Destination-SPACE/DS-Weather-Station-V4.5/docs/software/demo.rst

.. Copyright 2024 Destination SPACE Inc.
   Licensed under the Apache License, Version 2.0 (the "License");
   you may not use this file except in compliance with the License.
   You may obtain a copy of the License at

      http://www.apache.org/licenses/LICENSE-2.0

   Unless required by applicable law or agreed to in writing, software
   distributed under the License is distributed on an "AS IS" BASIS,
   WITHOUT WARRANTIES OR CONDITIONS OF ANY KIND, either express or implied.
   See the License for the specific language governing permissions and
   limitations under the License.

.. _demo-sketch:

Demo Sketch
===========

The `Demo <https://gitlab.com/Destination-SPACE/ds-weather-station-v4.5/-/blob/main/software/Demo/Demo.ino>`_ sketch is used as an introductory program to most of the features on the weather station. This includes scrollable menus for all sensors.

There is no data recording in this example.

Button Menu
-----------

On the weather station there are 4 buttons, ↑, ↓, ←, →.

The ← and → buttons are used to scroll between the weather menu, air quality menu, and the light menu.
