Destination-SPACE/DS-Weather-Station-V4.5/docs/activities/temperature.rst

.. Copyright 2024 Destination SPACE Inc.
   Licensed under the Apache License, Version 2.0 (the "License");
   you may not use this file except in compliance with the License.
   You may obtain a copy of the License at

      http://www.apache.org/licenses/LICENSE-2.0

   Unless required by applicable law or agreed to in writing, software
   distributed under the License is distributed on an "AS IS" BASIS,
   WITHOUT WARRANTIES OR CONDITIONS OF ANY KIND, either express or implied.
   See the License for the specific language governing permissions and
   limitations under the License.

.. _temperature:

Temperature Activity - Microclimates
====================================

Duration: 15 minutes

Background
----------

Materials
---------

- Destination Weather Station
- Paper
- Pencil

Procedure
---------

1. Make a map of the classroom on a sheet of paper. Make sure to label any windows, doors, air vents, and significant heat sources.
2. Make a prediction for which areas of the classroom you think will be hot or cold.
3. On your map, mark locations in the classroom you want to collect data.
4. Using your weather station, record the average temperature at each location you marked on your map.

Discussion Questions
--------------------

1. Did your predictions match the data you collected? Why might they be different?
2. What do you think caused that part of the classroom to be that temperature?
