Destination-SPACE/DS-Weather-Station-V4.5/docs/sensors/index.rst

.. Copyright 2024 Destination SPACE Inc.
   Licensed under the Apache License, Version 2.0 (the "License");
   you may not use this file except in compliance with the License.
   You may obtain a copy of the License at

      http://www.apache.org/licenses/LICENSE-2.0

   Unless required by applicable law or agreed to in writing, software
   distributed under the License is distributed on an "AS IS" BASIS,
   WITHOUT WARRANTIES OR CONDITIONS OF ANY KIND, either express or implied.
   See the License for the specific language governing permissions and
   limitations under the License.

.. _sensors:

Overview of Sensors
===================

The Destination Weather Station is equipped with a :ref:`Bosch BME280 combined humidity and pressure sensor<bme280>`.

In the expansion sensor kit, several more environmental sensors are provided to measure a wide variety of parameters. These include:

* :ref:`ScioSense ENS160 - Digital metal-oxide multi-gas sensor<ens160>`
* :ref:`Lite-On LTR390 - Ambient light and ultravoiolet light sensor<ltr390>`
* :ref:`Sensirion SCD40 - Miniature CO2 sensor<SCD40>`
* :ref:`Vishay VEML7700 - High accuracy ambient light sensor<veml7700>`
