Destination-SPACE/DS-Weather-Station-V4.5/docs/sensors/ens160.rst

.. Copyright 2024 Destination SPACE Inc.
   Licensed under the Apache License, Version 2.0 (the "License");
   you may not use this file except in compliance with the License.
   You may obtain a copy of the License at

      http://www.apache.org/licenses/LICENSE-2.0

   Unless required by applicable law or agreed to in writing, software
   distributed under the License is distributed on an "AS IS" BASIS,
   WITHOUT WARRANTIES OR CONDITIONS OF ANY KIND, either express or implied.
   See the License for the specific language governing permissions and
   limitations under the License.

.. _ens160:

ENS160
======

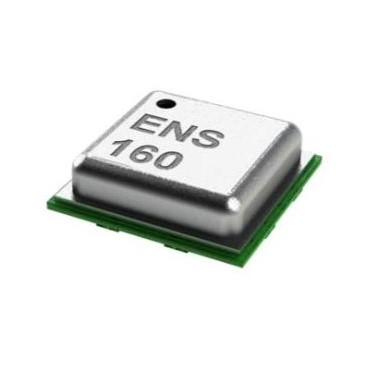
[picture p20: docs/assets/MFG_ENS160.jpg]


The ENS160 digital metal-oxide multi-gas sensor measures volitile organic compounds (VOCs), which can be used to measure total VOC content (TVOC), air quality index (AQI), and calculate an approximate value for carbon-dioxide concentration (eCO2).

Specifications
~~~~~~~~~~~~~~

.. list-table::
   :header-rows: 1

   * - Parameter
     - Range
     - Resolution
     - Units

   * - TVOC
     - 0 - 65,000
     - 1
     - ppb

   * - eCO2
     - 400 - 65,000
     - 1
     - ppm CO2 equivalent

   * - AQI-UBA
     - 1 to 5
     - 1
     - -

   * - AQI-EPA
     - 0 - 500
     - 1
     - -

TVOC
~~~~
Total Volitile Organic Compounds (TVOC) is a useful parameter used to determine the quality of the air in a given area. This is incredibly important for urban environments and in indoor settings. This is typically measured in parts-per-billion (ppb), but in polluted environments, can reach into the parts-per-million (ppm) range.

eCO2
~~~~
The ENS160 sensor uses an algorythm to calculate an approximate value for carbon-dioxide (CO2) concentration. While the sensor cannot directly measure CO2, it's algorythm can closely approximate this value, as seen in the graph below.

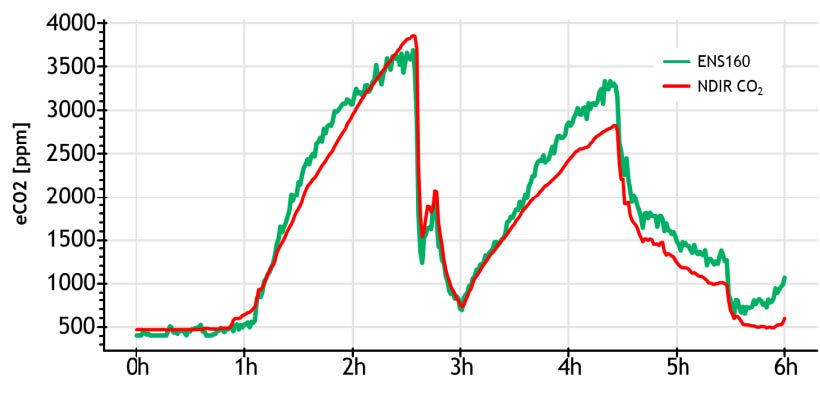
[picture p21: docs/assets/ens160_eco2.jpg]


In the graph, the calculated eCO2 measurment is being compared to a nondispersive infrared CO2 sensor. It can closely approximate the CO2 concentration, but it is not perfect.

In the graphs below, ScioSense has provided eCO2 measurments for different environments, such as in a bedroom, kitchen, and bathroom. These graphs show that different conditions, such as closing a window, cooking, or being in a room can increase CO2 concentrations.

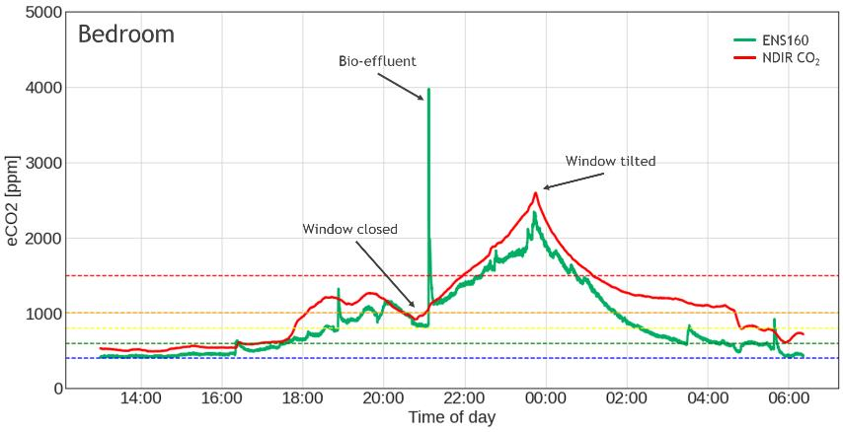
[picture p22: docs/assets/ens160_eco2_bedroom.jpg]


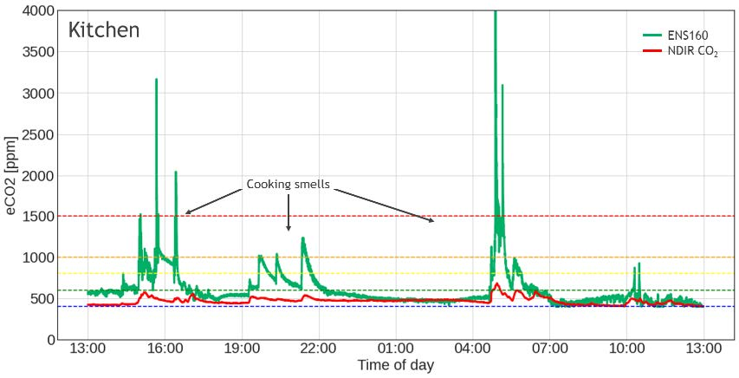
[picture p23: docs/assets/ens160_eco2_kitchen.jpg]


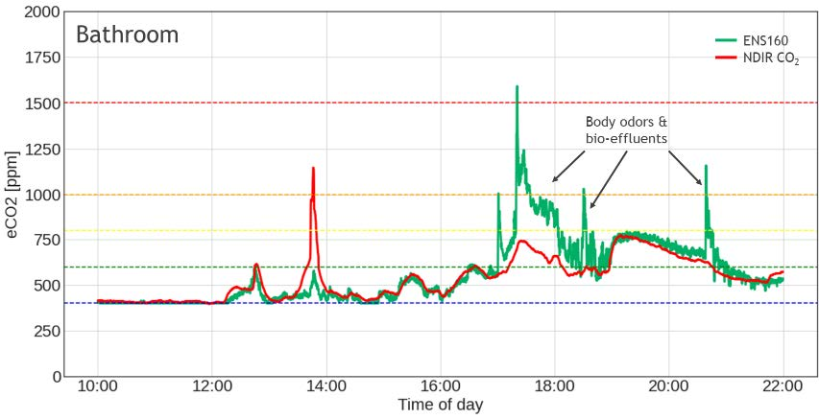
[picture p24: docs/assets/ens160_eco2_bathroom.jpg]


AQI
~~~
Air Quality Index (AQI) is the typical parameter used to judge the quality of air and how polluted it is. There are several different scales used to measure this value, but they are all based on the concentration of VOCs. For example, the United States uses the `NowCast <https://www.airnow.gov/aqi/aqi-basics/>`_ algorythm developed by the Environmental Protection Agency (EPA) ranging from 0 to 500, the European Union's `European Environment Agency <https://airindex.eea.europa.eu/AQI/index.html>`_ (EEA) uses a scale ranging from 0 to 1250, and Taiwan's `Ministry of Environment <https://airtw.epa.gov.tw/ENG/Information/Standard/AirQualityIndicator.aspx>`_ uses a similar scale to the United States, ranging from 0 to 500. The figures below show each of these indexes.

Environmental Protection Agency (EPA)

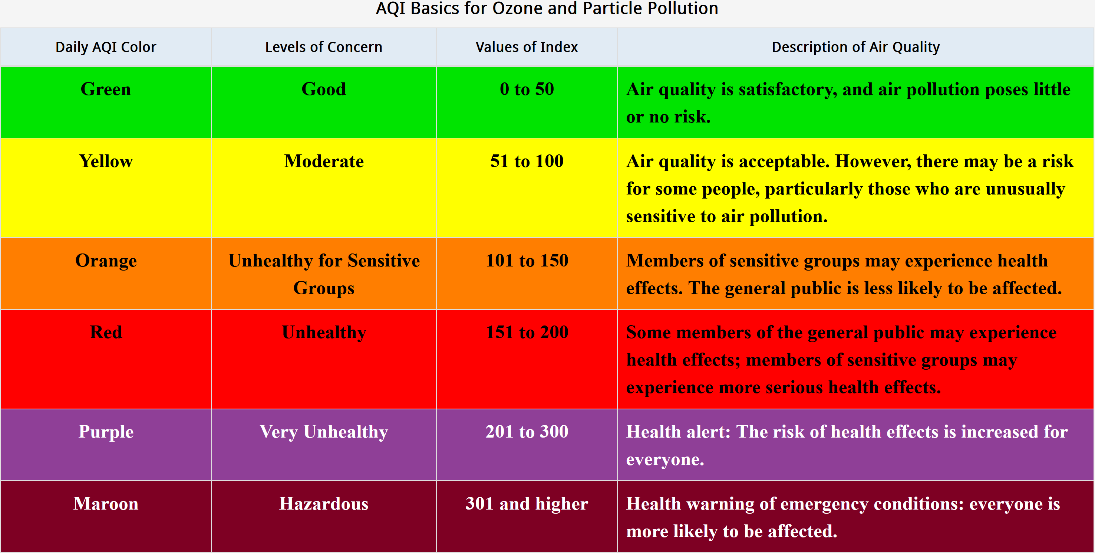
[picture p25: docs/assets/aqi_us.png]


European Environment Agency (EEA)

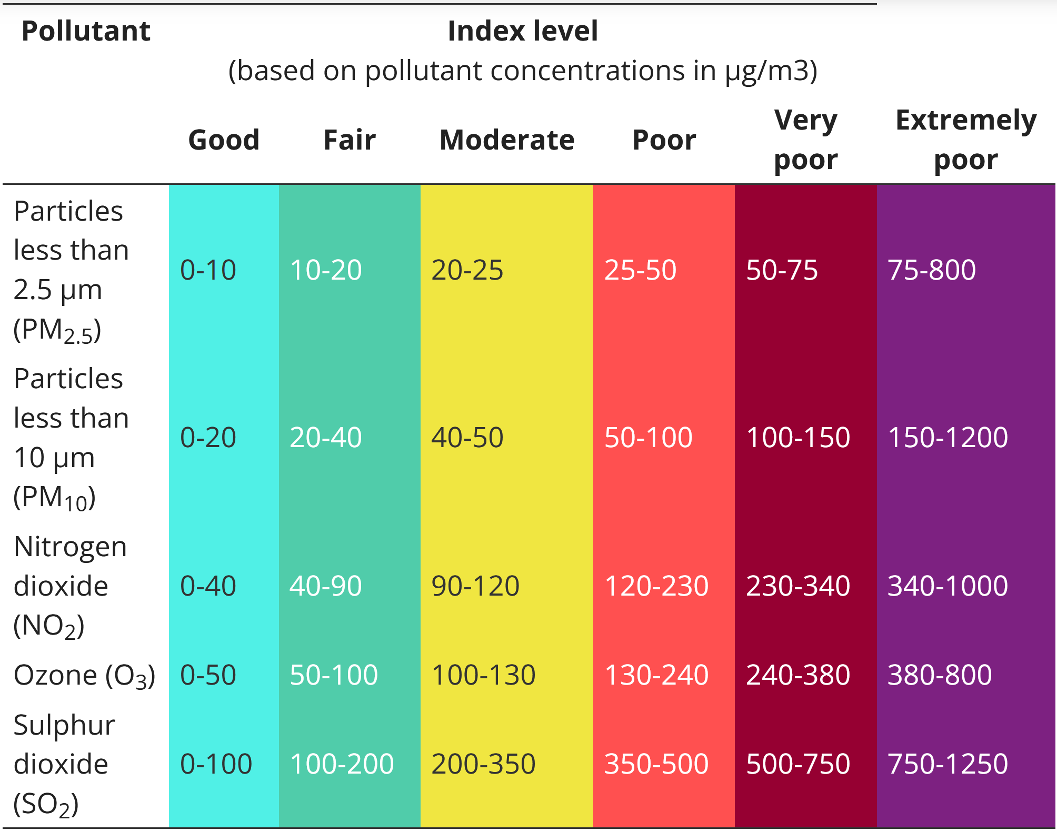
[picture p26: docs/assets/aqi_eu.png]


Ministry of Environment

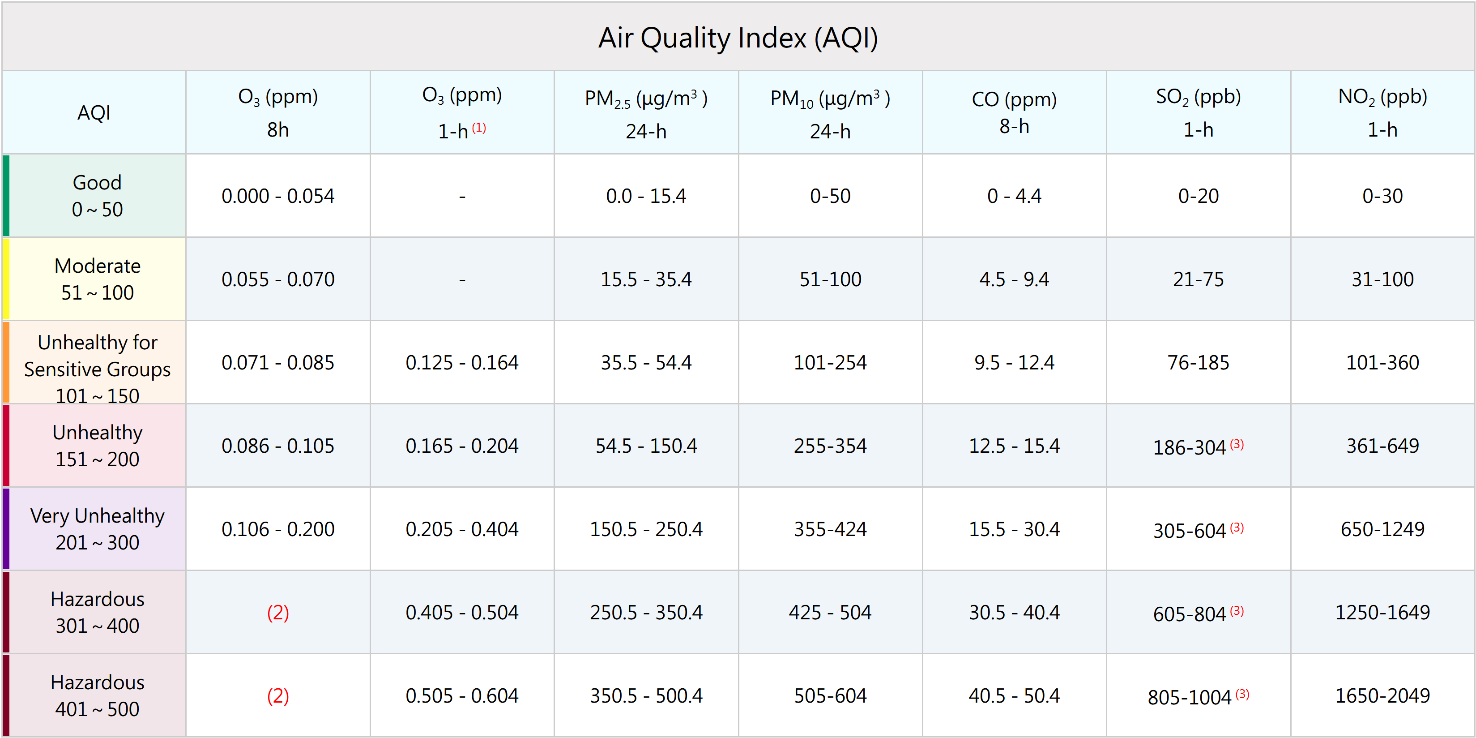
[picture p27: docs/assets/aqi_tw.png]
