Destination-SPACE/DS-Weather-Station-V4.5/docs/assets/unpopulated.png

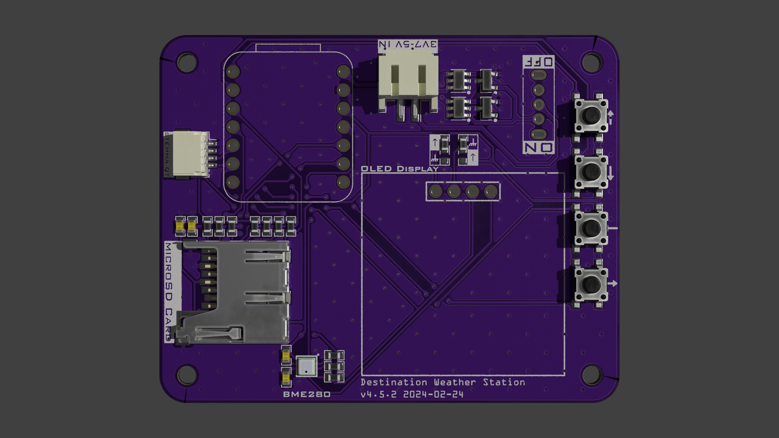
docs/assets/unpopulated.png
